Sevcav/dice-tracker/Dice Images/6 Sided angle 1.jpg

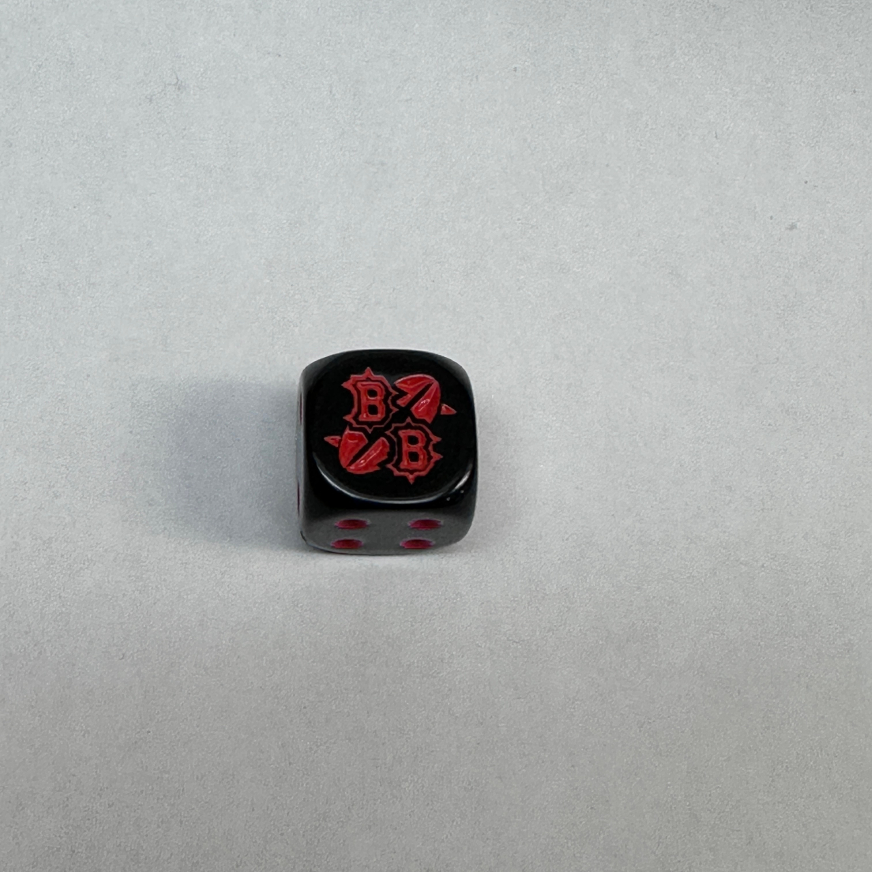
Dice Images/6 Sided angle 1.jpg
