Sevcav/dice-tracker/Dice Images/6 sided angle 3.jpg

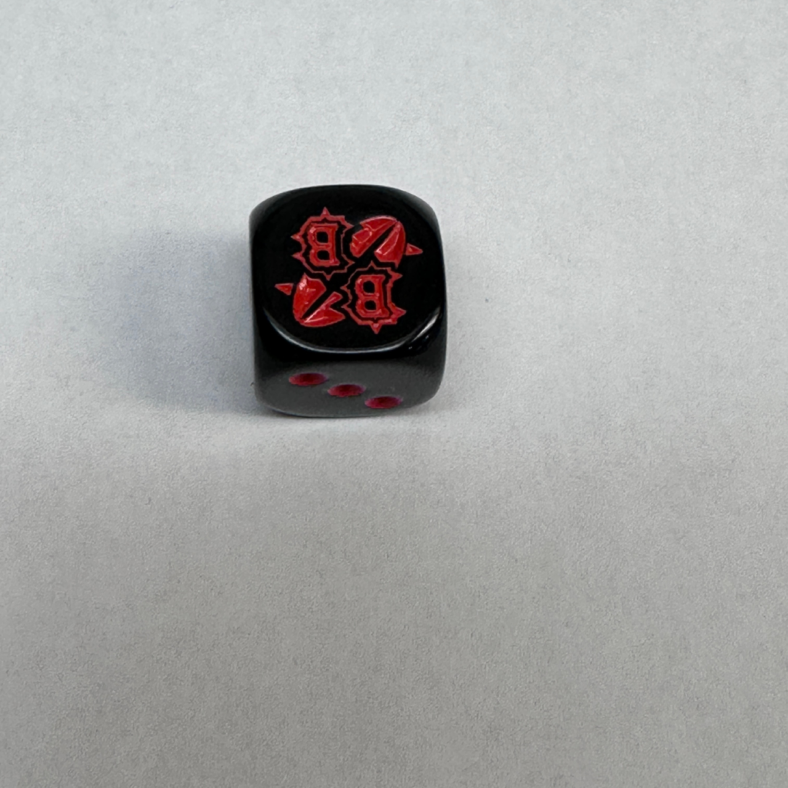
Dice Images/6 sided angle 3.jpg
