Sevcav/dice-tracker/Dice Images/6 sided angle 4.jpg

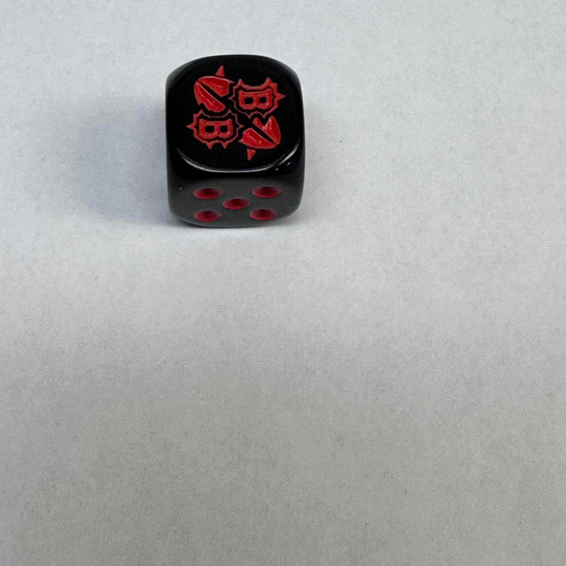
Dice Images/6 sided angle 4.jpg
