Sevcav/dice-tracker/Dice Images/6 Sided Top.jpg

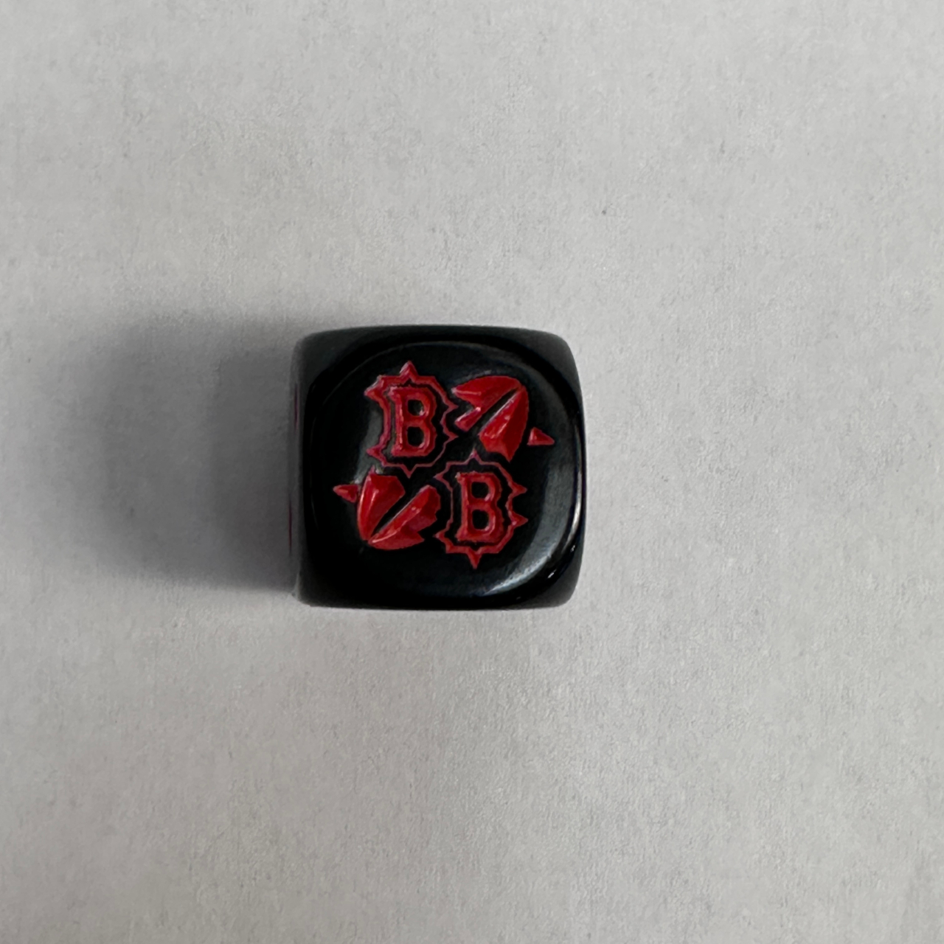
Dice Images/6 Sided Top.jpg
