Sevcav/dice-tracker/Dice Images/6 sidesd angle 2.jpg

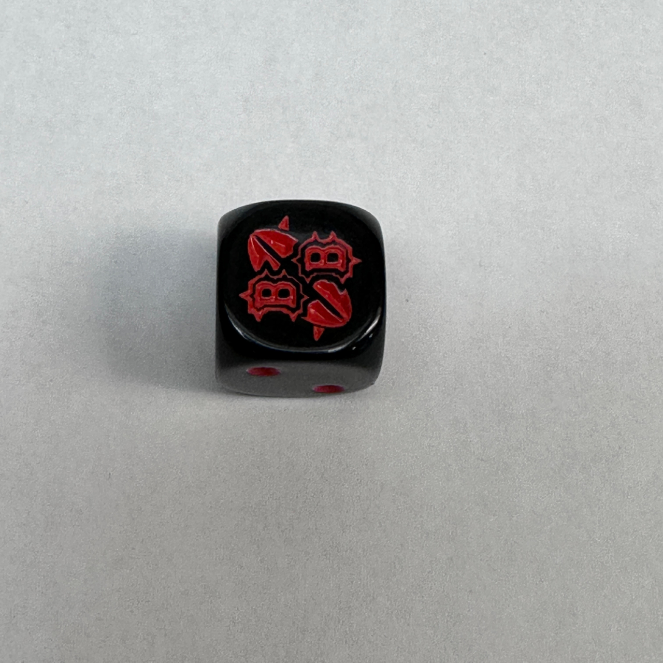
Dice Images/6 sidesd angle 2.jpg
