Sevcav/dice-tracker/Dice Images/8 Sided.jpg

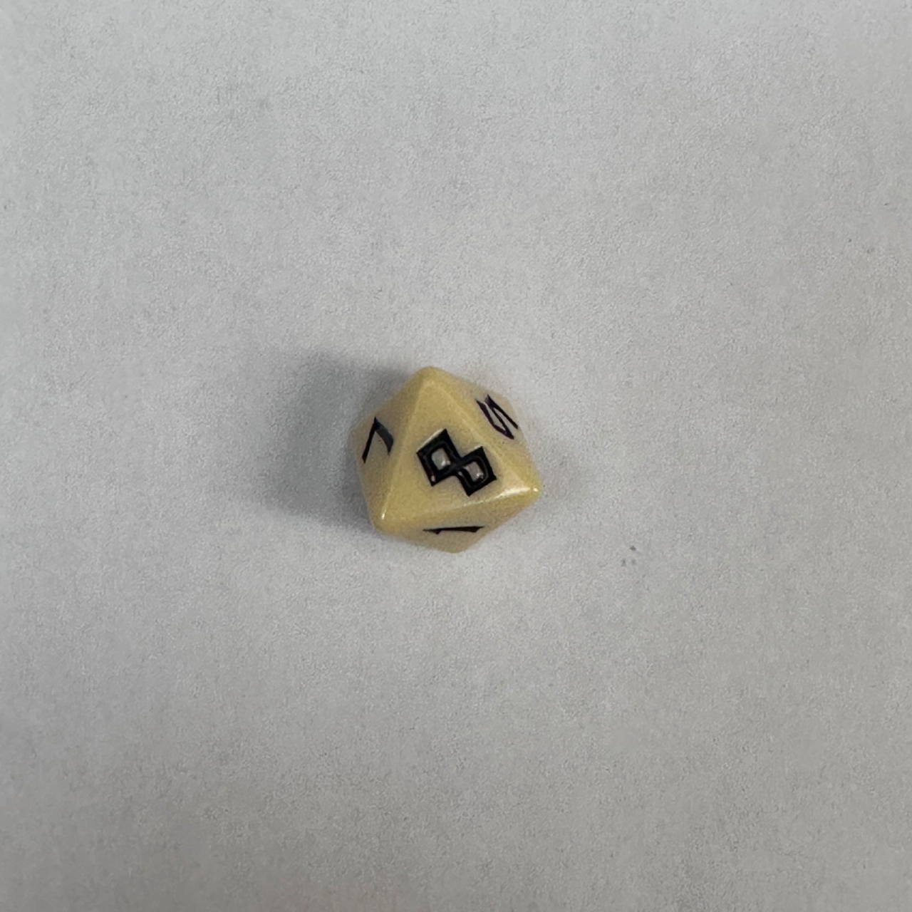
Dice Images/8 Sided.jpg
