Sevcav/dice-tracker/Dice Images/16 sided.jpg

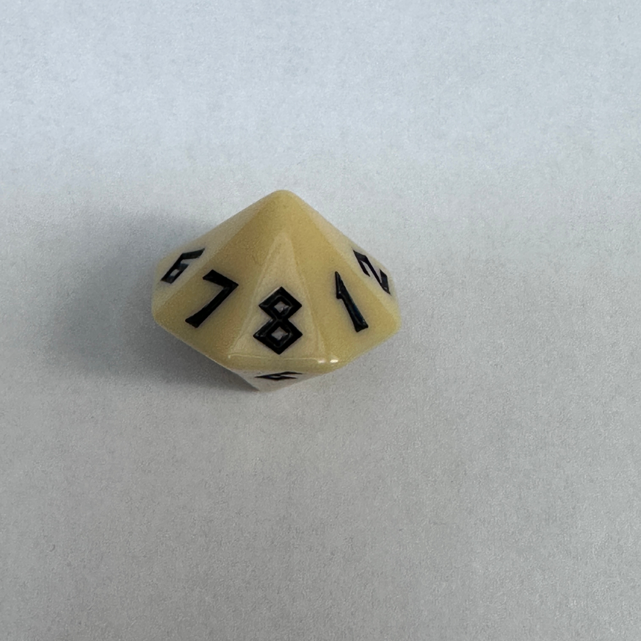
Dice Images/16 sided.jpg
