Sevcav/dice-tracker/Dice Images/Both Down Face.jpg

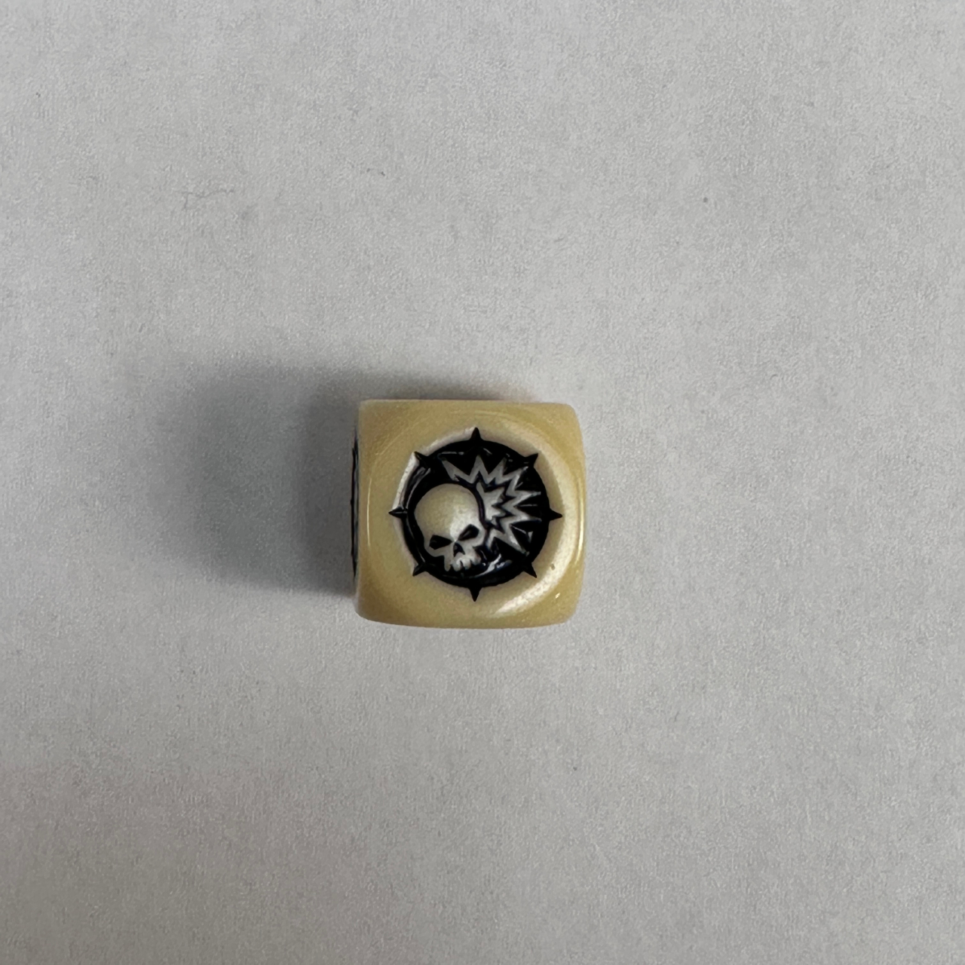
Dice Images/Both Down Face.jpg
