Sevcav/dice-tracker/Dice Images/Player Down Angle 1.jpg

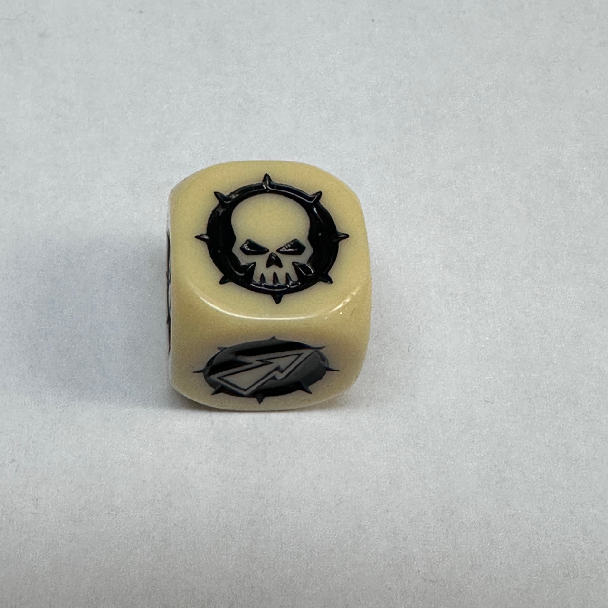
Dice Images/Player Down Angle 1.jpg
