Sevcav/dice-tracker/Dice Images/Player Down Angle 2.jpg

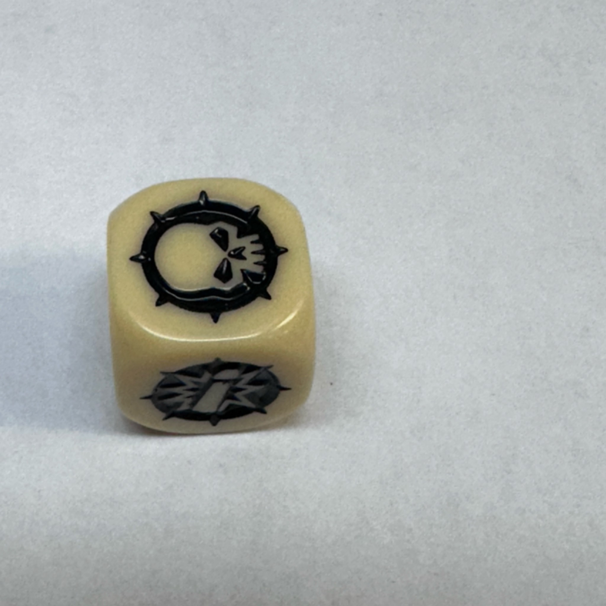
Dice Images/Player Down Angle 2.jpg
