Sevcav/dice-tracker/Dice Images/Player Down Angle 3.jpg

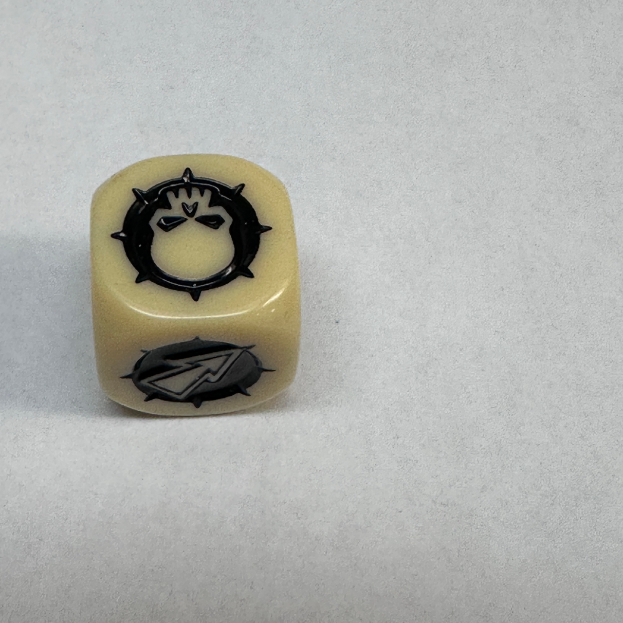
Dice Images/Player Down Angle 3.jpg
