Sevcav/dice-tracker/Dice Images/Player Down Angle 4.jpg

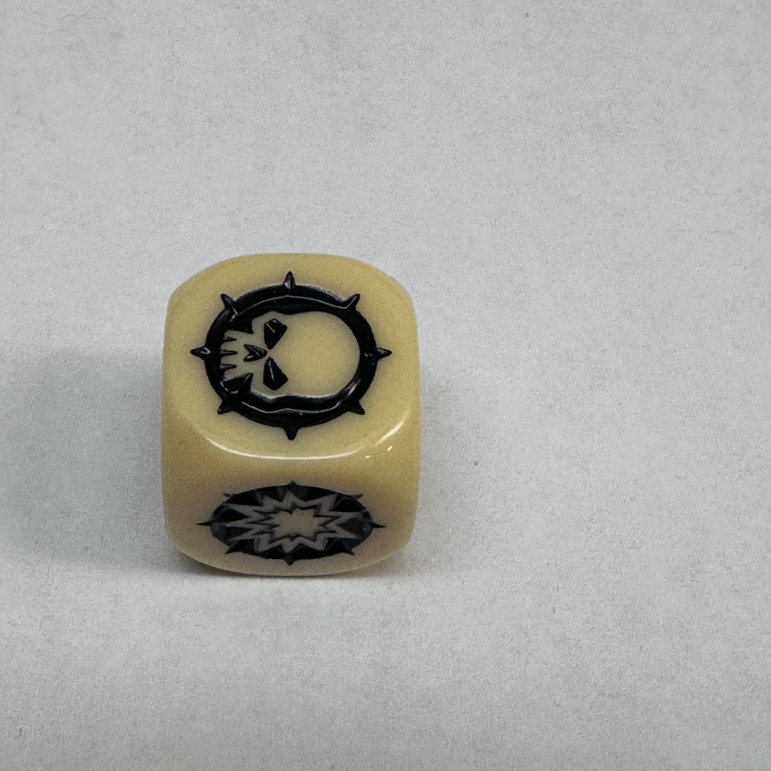
Dice Images/Player Down Angle 4.jpg
