Sevcav/dice-tracker/Dice Images/Player Down Face.jpg

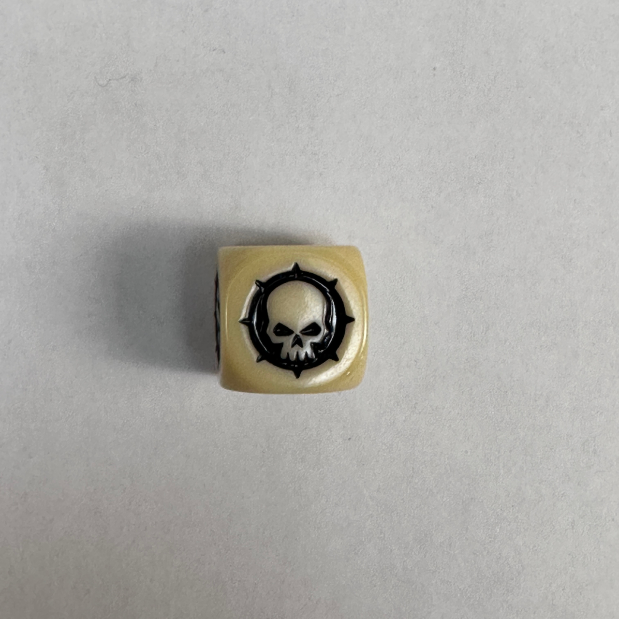
Dice Images/Player Down Face.jpg
