Sevcav/dice-tracker/Dice Images/POW Angle 1.jpg

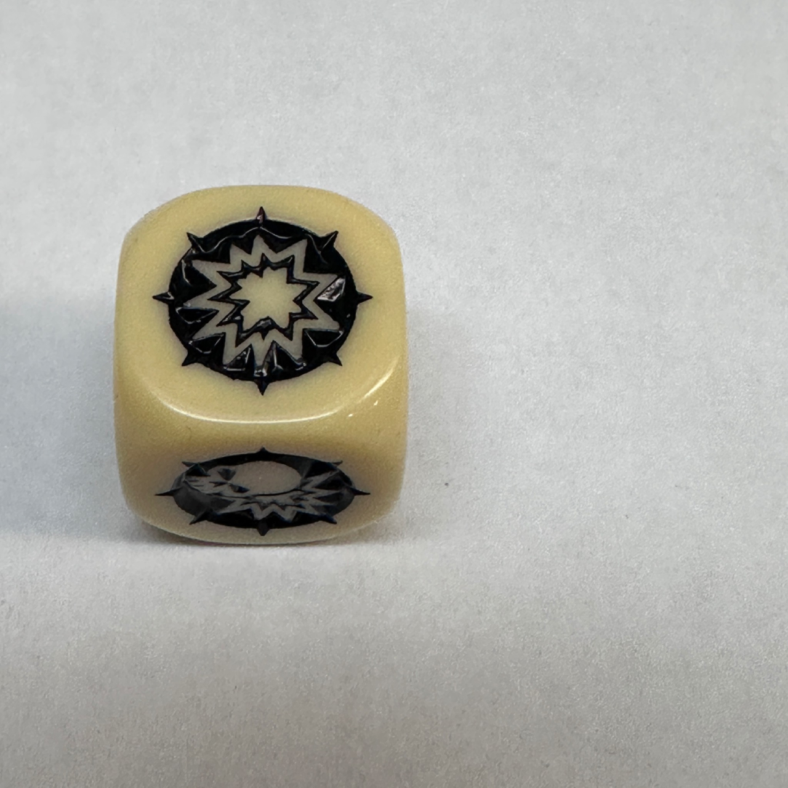
Dice Images/POW Angle 1.jpg
