Sevcav/dice-tracker/Dice Images/POW Angle 2.jpg

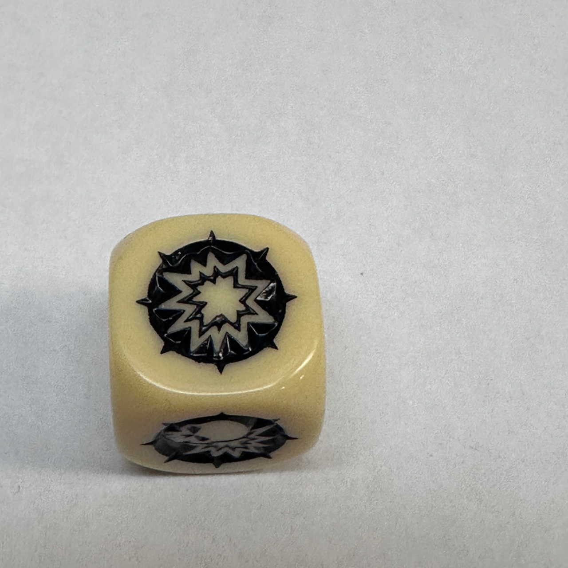
Dice Images/POW Angle 2.jpg
