Sevcav/dice-tracker/Dice Images/POW Angle 3.jpg

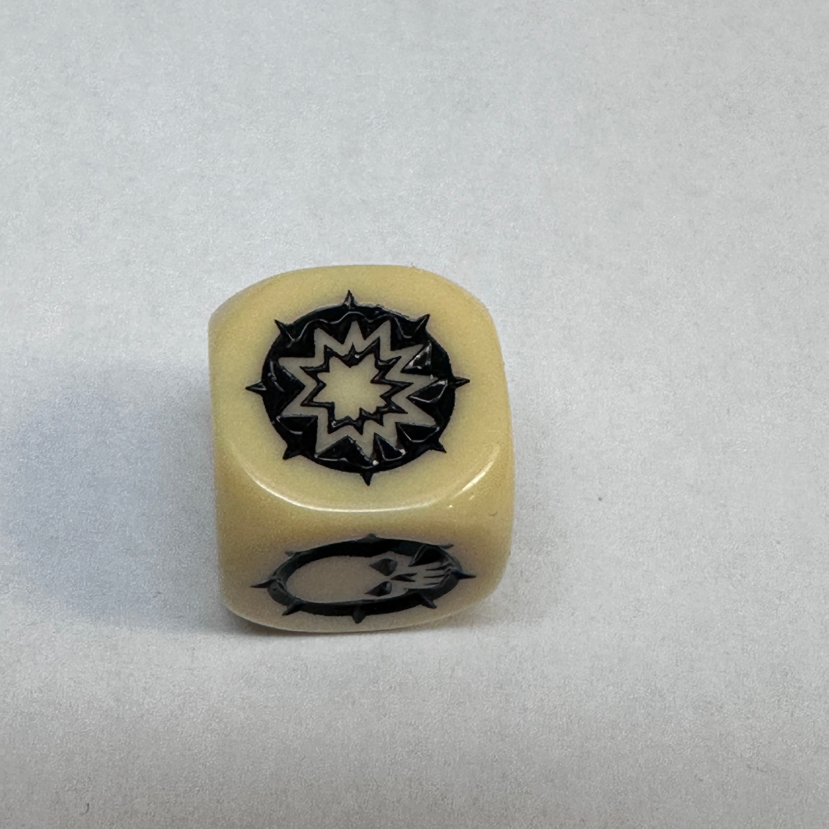
Dice Images/POW Angle 3.jpg
