Sevcav/dice-tracker/Dice Images/POW Angle 4.jpg

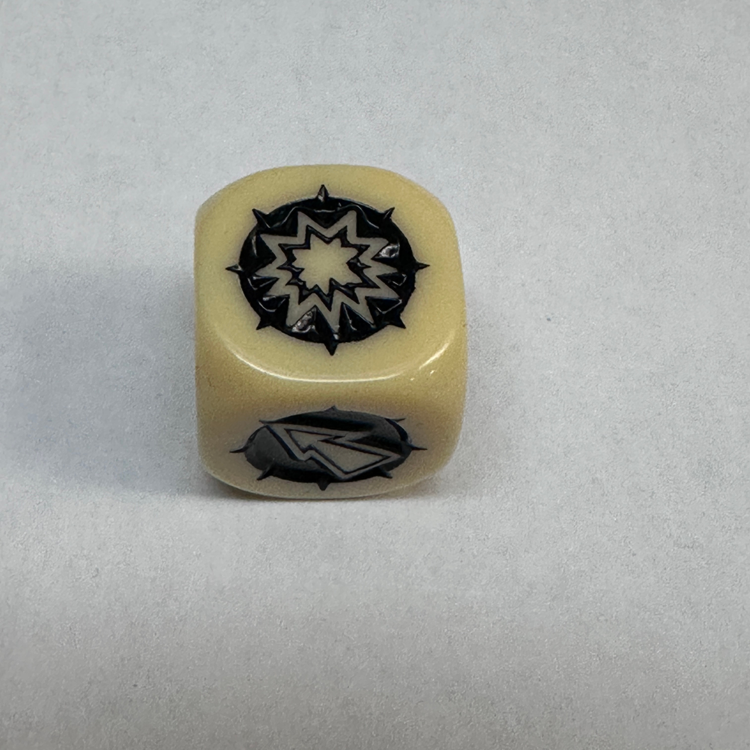
Dice Images/POW Angle 4.jpg
