Sevcav/dice-tracker/Dice Images/POW Face.jpg

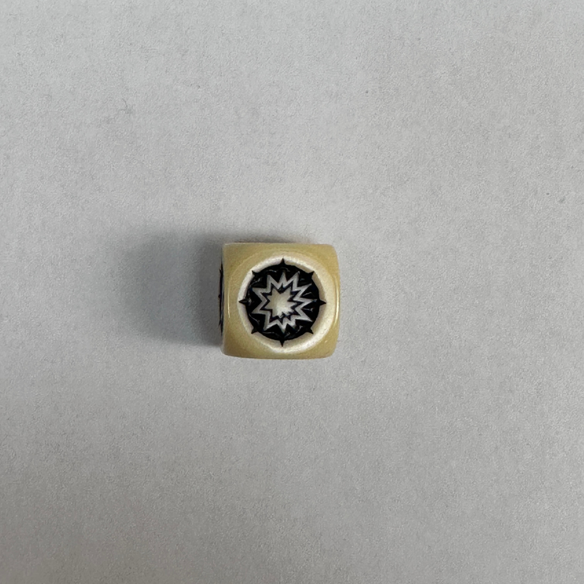
Dice Images/POW Face.jpg
