Sevcav/dice-tracker/Dice Images/Push Angle 1.jpg

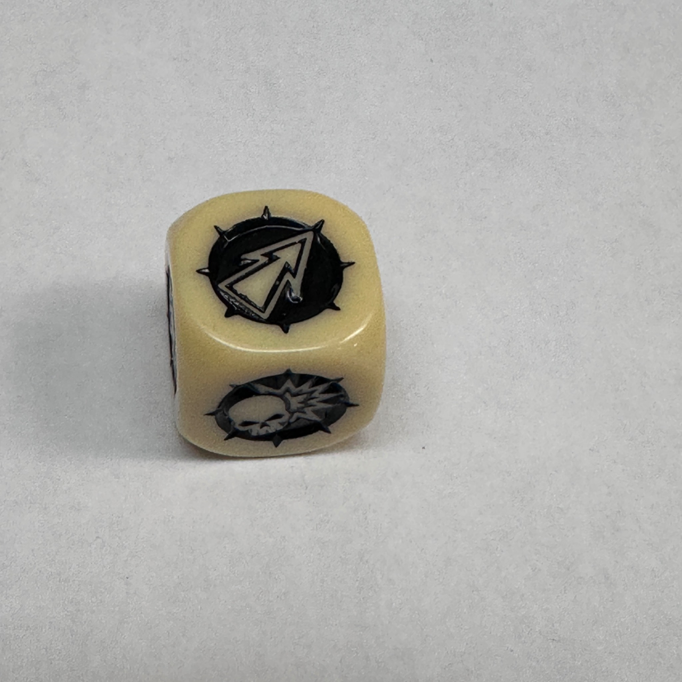
Dice Images/Push Angle 1.jpg
