Sevcav/dice-tracker/Dice Images/Push Angle 2.jpg

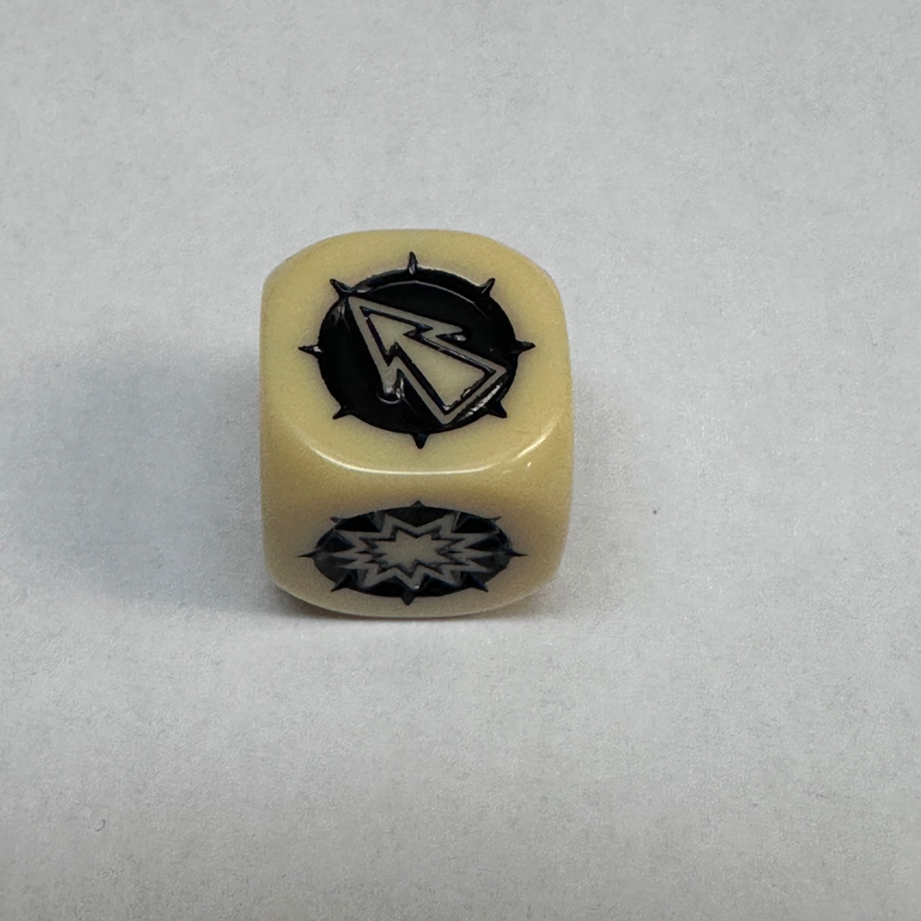
Dice Images/Push Angle 2.jpg
