Sevcav/dice-tracker/Dice Images/Push Angle 4.jpg

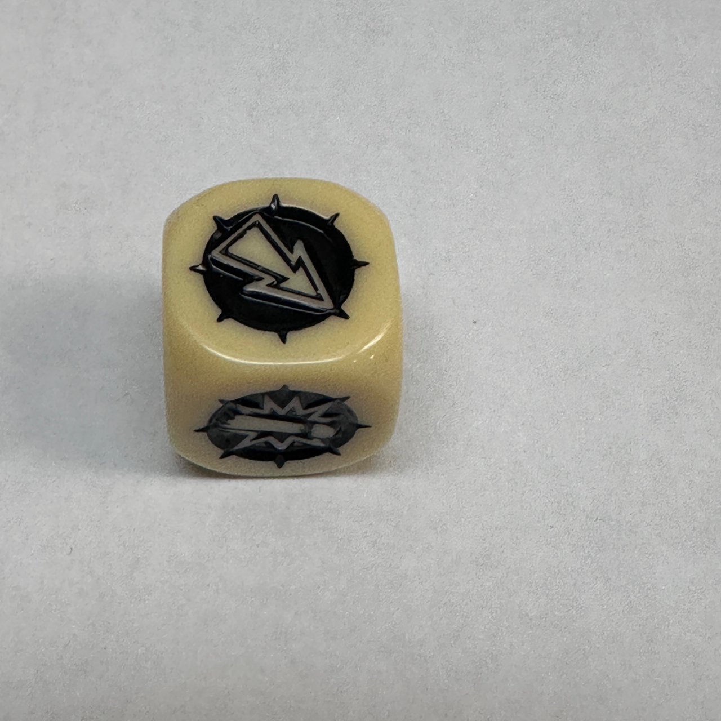
Dice Images/Push Angle 4.jpg
