Sevcav/dice-tracker/Dice Images/Push Face.jpg

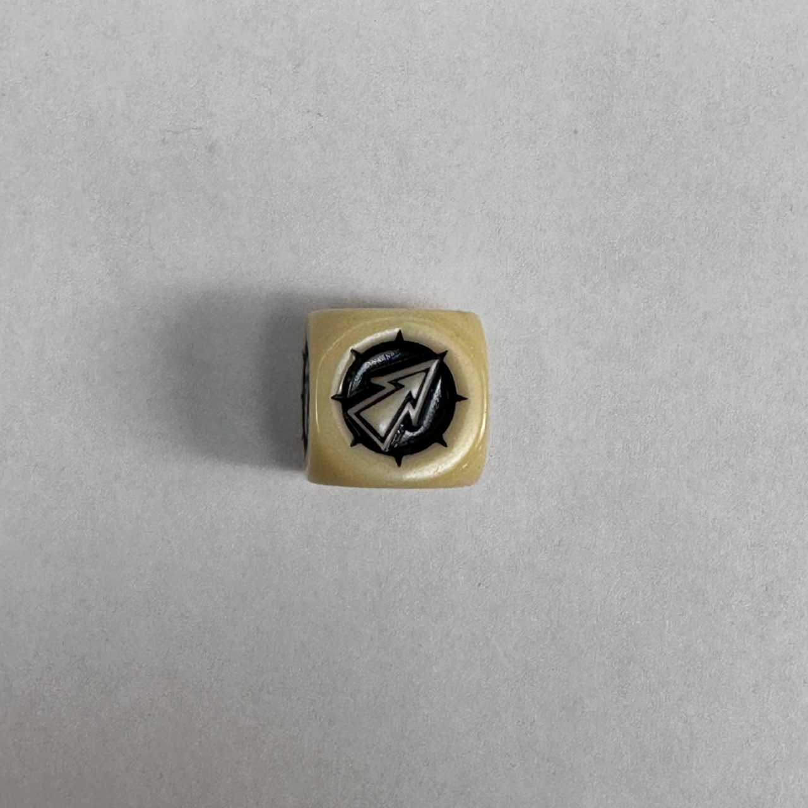
Dice Images/Push Face.jpg
