Sevcav/dice-tracker/Dice Images/Stumble Angel 4.jpg

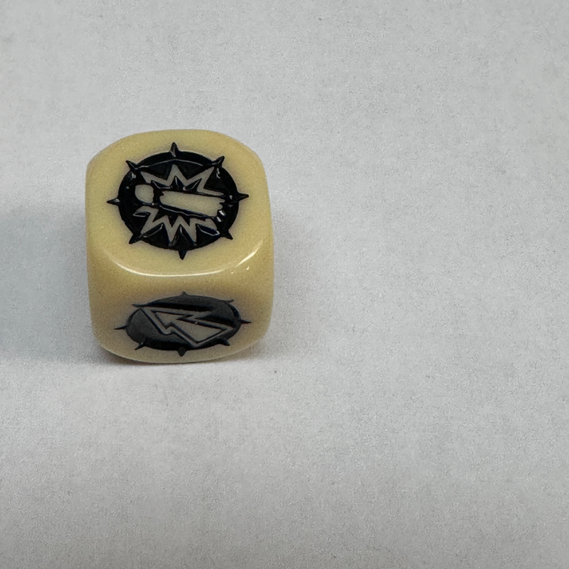
Dice Images/Stumble Angel 4.jpg
