Sevcav/dice-tracker/Dice Images/Stumble Angle 1.jpg

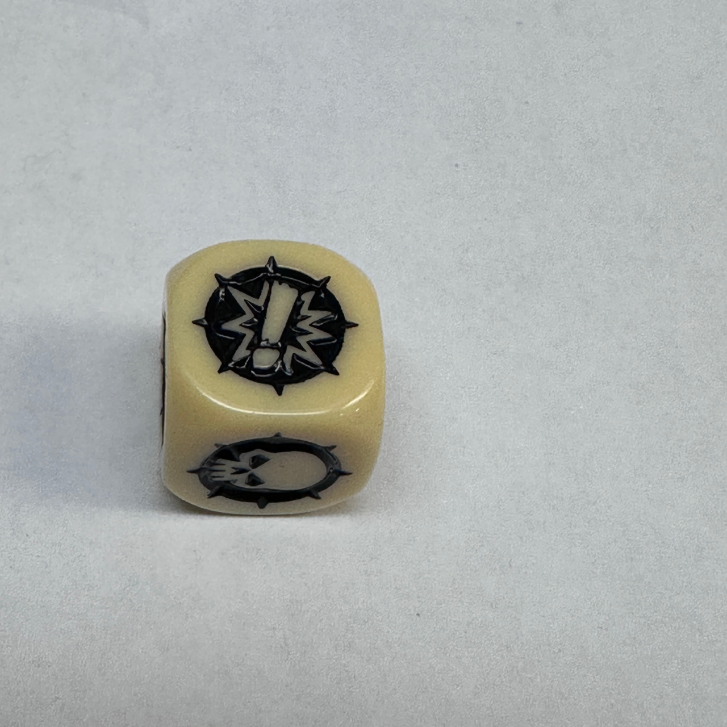
Dice Images/Stumble Angle 1.jpg
