Sevcav/dice-tracker/Dice Images/Stumble Angle 2.jpg

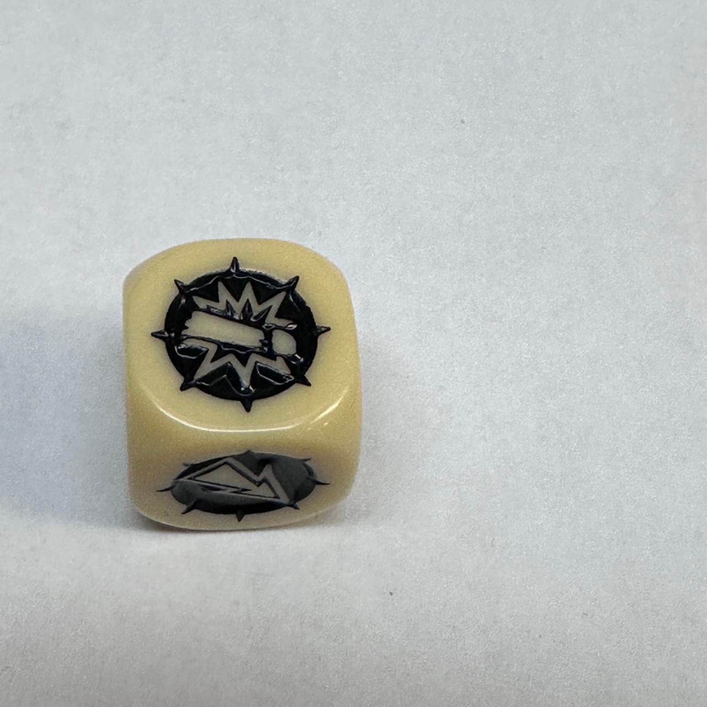
Dice Images/Stumble Angle 2.jpg
