Sevcav/dice-tracker/Dice Images/Stumble Angle 3.jpg

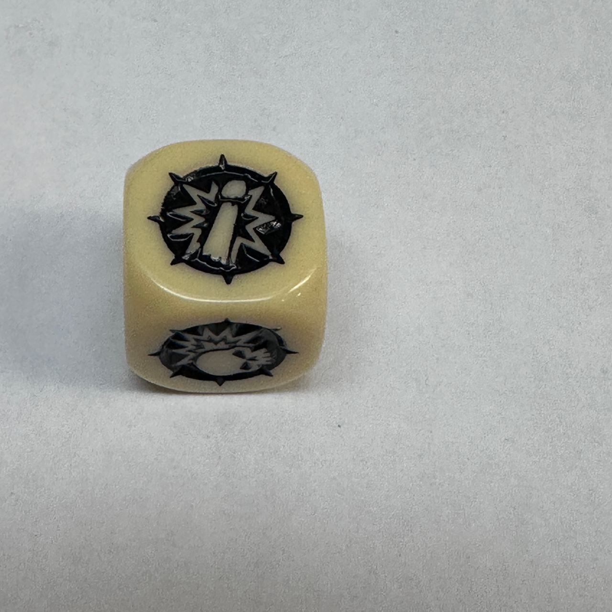
Dice Images/Stumble Angle 3.jpg
