Sevcav/dice-tracker/Dice Images/Stumble Face.jpg

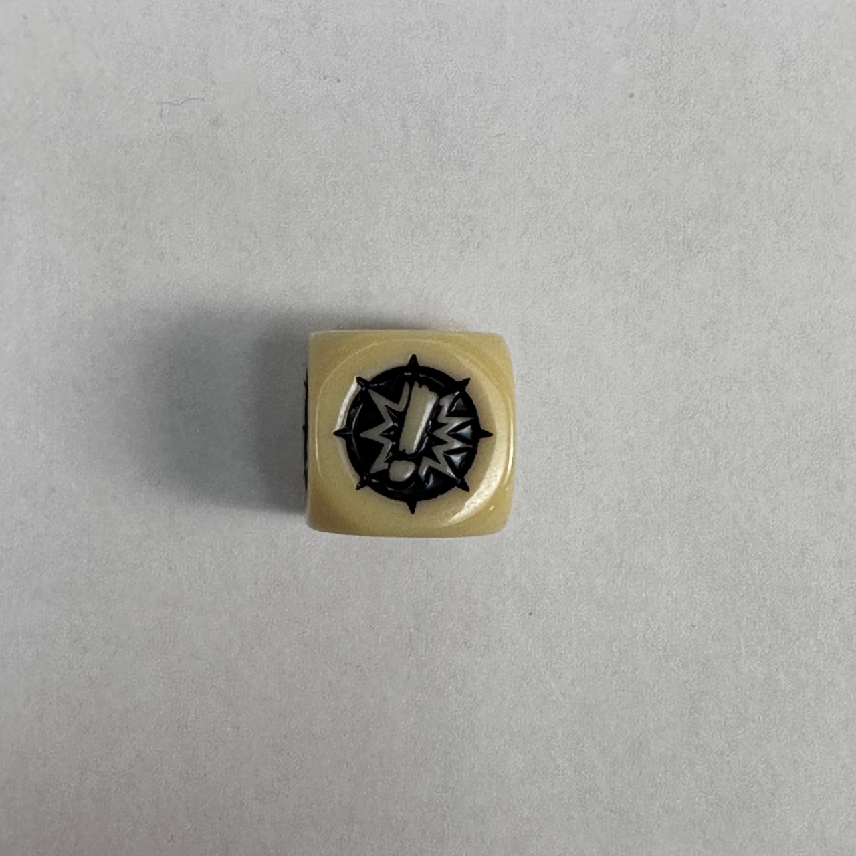
Dice Images/Stumble Face.jpg
